HabonRoof/SCR-Charging/AD5940_BATImpedance/ADICUP3029/ADICUP3029Port.c

/*!
 *****************************************************************************
 @file:    ADICUP3029Port.c
 @author:  Neo Xu
 @brief:   The port for ADI's ADICUP3029 board.
 -----------------------------------------------------------------------------

Copyright (c) 2017-2019 Analog Devices, Inc. All Rights Reserved.

This software is proprietary to Analog Devices, Inc. and its licensors.
By using this software you agree to the terms of the associated
Analog Devices Software License Agreement.

*****************************************************************************/

#include <AD5940.h>
#include "ADuCM3029.h"
#include <stdlib.h>

#define SYSTICK_MAXCOUNT ((1L<<24)-1) /* we use Systick to complete function Delay10uS(). This value only applies to ADICUP3029 board. */
#define SYSTICK_CLKFREQ   26000000L   /* Systick clock frequency in Hz. This only appies to ADICUP3029 board */
volatile static uint32_t ucInterrupted = 0;       /* Flag to indicate interrupt occurred */
volatile static uint32_t rxBufIdx = 0;

extern char recvData[32];     // Data from SCIA RX
extern char recvBuff[32];
extern bool frecvFreq, NL, freqUpdate;
extern float recvFloat;


/**
	@brief Using SPI to transmit N bytes and return the received bytes. This function targets to 
         provide a more efficient way to transmit/receive data.
	@param pSendBuffer :{0 - 0xFFFFFFFF}
      - Pointer to the data to be sent.
	@param pRecvBuff :{0 - 0xFFFFFFFF}
      - Pointer to the buffer used to store received data.
	@param length :{0 - 0xFFFFFFFF}
      - Data length in SendBuffer.
	@return None.
**/
void AD5940_ReadWriteNBytes(unsigned char *pSendBuffer,unsigned char *pRecvBuff,unsigned long length)
{
  uint32_t tx_count=0, rx_count=0;
  pADI_SPI0->CNT = length;
  while(1){
    uint32_t fifo_sta = pADI_SPI0->FIFO_STAT;
    if(rx_count < length){
      if(fifo_sta&0xf00){//there is data in RX FIFO.
        *pRecvBuff++ = pADI_SPI0->RX;
        rx_count ++;
      }
    }
    if(tx_count < length){
      if((fifo_sta&0xf) < 8){// there is space in TX FIFO.
        pADI_SPI0->TX = *pSendBuffer++;
        tx_count ++;
      }
    }
    if(rx_count == length && tx_count==length)
      break;  //done
  }
  while((pADI_SPI0->STAT&BITM_SPI_STAT_XFRDONE) == 0);//wait for transfer done.
}

void AD5940_CsClr(void)
{
   pADI_GPIO1->CLR = (1<<10);
}

void AD5940_CsSet(void)
{
   pADI_GPIO1->SET = (1<<10);
}

void AD5940_RstSet(void)
{
   pADI_GPIO2->SET = 1<<6; //p2.6-ADC3-A3
}

void AD5940_RstClr(void)
{
   pADI_GPIO2->CLR = 1<<6; //p2.6-ADC3-A3
}

void AD5940_Delay10us(uint32_t time)
{
  if(time==0)return;
  if(time*10<SYSTICK_MAXCOUNT/(SYSTICK_CLKFREQ/1000000)){
    SysTick->LOAD = time*10*(SYSTICK_CLKFREQ/1000000);
    SysTick->CTRL = (1 << 2) | (1<<0);    /* Enable SysTick Timer, using core clock */
    while(!((SysTick->CTRL)&(1<<16)));    /* Wait until count to zero */
    SysTick->CTRL = 0;                    /* Disable SysTick Timer */
  }
  else {
    AD5940_Delay10us(time/2);
    AD5940_Delay10us(time/2 + (time&1));
  }
}

uint32_t AD5940_GetMCUIntFlag(void)
{
   return ucInterrupted;
}

uint32_t AD5940_ClrMCUIntFlag(void)
{
   pADI_XINT0->CLR = BITM_XINT_CLR_IRQ0;
   ucInterrupted = 0;
   return 1;
}

/* This function is used to set Dn on Arduino shield(and set it to output) */
void Arduino_WriteDn(uint32_t Dn, BoolFlag bHigh)
{
  if(Dn&(1<<3)) //set D3, P0.13
  {
    pADI_GPIO0->OEN |=  1<<13;
    if(bHigh)
      pADI_GPIO0->SET = 1<<13;
    else 
      pADI_GPIO0->CLR = 1<<13;
  }
  if(Dn&(1<<4))//Set D4, P0.9
  {
    pADI_GPIO0->OEN |=  1<<9;
    if(bHigh)
      pADI_GPIO0->SET = 1<<9;
    else 
      pADI_GPIO0->CLR = 1<<9;
  }
}

/* Functions that used to initialize MCU platform */

uint32_t AD5940_MCUResourceInit(void *pCfg)
{
  /* Step1, initialize SPI peripheral and its GPIOs for CS/RST */
  pADI_GPIO0->PE = 0xFFFF;
  pADI_GPIO1->PE = 0xFFFF;
  pADI_GPIO2->PE = 0xFFFF;
  pADI_GPIO2->OEN |= (1<<6); //P2.6-ADC3-A3-AD5940_Reset
  pADI_GPIO2->SET = 1<<6; //Pull high this pin.

  /*Setup Pins P0.0-->SCLK P0.1-->MOSI P0.2-->MISO P1.10-->CS*/
  pADI_GPIO0->CFG = (1<<0)|(1<<2)|(1<<4)|(pADI_GPIO0->CFG&(~((3<<0)|(3<<2)|(3<<4))));
  pADI_GPIO1->CFG &=~(3<<14); /* Configure P1.10 to GPIO function */
  pADI_GPIO1->OEN |= (1<<10); /* P1.10 Output Enable */
  /*Set SPI Baudrate = PCLK/2x(iCLKDiv+1).*/
  pADI_SPI0->DIV = 0;/*Baudrae is 13MHz*/
  pADI_SPI0->CTL = BITM_SPI_CTL_CSRST|        // Configure SPI to reset after a bit shift error is detected
      BITM_SPI_CTL_MASEN|                   // Enable master mode
      /*BITM_SPI_CTL_CON|*/                     // Enable continous transfer mode
         BITM_SPI_CTL_OEN|                     // Select MISO pin to operate as normal -
            BITM_SPI_CTL_RXOF|                    // overwrite data in Rx FIFO during overflow states
               /*BITM_SPI_CTL_ZEN|*/                     // transmit 00 when no valid data in Tx FIFO
                  BITM_SPI_CTL_TIM|                     // initiate trasnfer with a write to SPITX
                     BITM_SPI_CTL_SPIEN;                  // Enable SPI. SCLK idles low/ data clocked on SCLK falling edge
  pADI_SPI0->CNT = 1;// Setup to transfer 1 bytes to slave
  /* Step2: initialize GPIO interrupt that connects to AD5940's interrupt output pin(Gp0, Gp3, Gp4, Gp6 or Gp7 ) */
  pADI_GPIO0->IEN |= 1<<15;// Configure P0.15 as an input

  pADI_XINT0->CFG0 = (0x1<<0)|(1<<3);//External IRQ0 enabled. Falling edge
	
  pADI_XINT0->CLR = BITM_XINT_CLR_IRQ0;
  NVIC_EnableIRQ(XINT_EVT0_IRQn);		  //Enable External Interrupt 0 source.

  AD5940_CsSet();
  AD5940_RstSet();
  return 0;
}

/* MCU related external line interrupt service routine */
void Ext_Int0_Handler()
{
   pADI_XINT0->CLR = BITM_XINT_CLR_IRQ0;
   ucInterrupted = 1;
  /* This example just set the flag and deal with interrupt in AD5940Main function. It's your choice to choose how to process interrupt. */
}

/* UART Rx interrupt service routine */
void UART_Int_Handler()
{
		unsigned char c;
		c = pADI_UART0->RX;			// Read UART0 RX buffer can automatically reset interrupt flag
		recvBuff[rxBufIdx] = c;
		rxBufIdx++;
		if(c == '\n'){					// If received '\n' char
			NL = true;					// set NL flag
			memset(recvData, 0, sizeof(recvData));		// Clear data
			strcpy(recvData,recvBuff);								// Copy Rx buffer to data
			if(frecvFreq){											// If receive "f\n" string
					frecvFreq = false;
					freqUpdate = true;
					int i = 0;
					for(i = 0; i < 4; i++)
							*((char*)&recvFloat + i) = recvBuff[i];		// Put 4 byte data into float variable
			}
			memset(recvBuff, 0, sizeof(recvBuff));		// Clear buffer
			rxBufIdx = 0;														// Reset buffer index
		}
		if(recvData[0] == 'f' && recvData[1] == '\n')	// If string is "f\n"
			frecvFreq = true;
}
